kisbAlt/espSkipper_v2/espSkipper2_firmware/src/display/David_Sans8pt7b.h

const uint8_t David_Sans8pt7bBitmaps[] PROGMEM = {
  0x00, 0xFF, 0xFF, 0xFF, 0x0F, 0xCF, 0x3C, 0xF3, 0x30, 0xC3, 0x0C, 0x30,
  0xC3, 0x0C, 0xFF, 0xFF, 0xFF, 0x30, 0xC3, 0x0C, 0xFF, 0xFF, 0xFF, 0x30,
  0xC3, 0x0C, 0x30, 0xC3, 0x0C, 0x0C, 0x03, 0x03, 0xF0, 0xFC, 0xCC, 0xF3,
  0x3C, 0xC3, 0x30, 0x3C, 0x0F, 0x00, 0xF0, 0x3C, 0x0C, 0xC3, 0x3C, 0xCF,
  0x33, 0x3F, 0x0F, 0xC0, 0xC0, 0x30, 0x30, 0x30, 0x30, 0x30, 0xCC, 0x30,
  0xCC, 0x30, 0xCC, 0xC0, 0xCC, 0xC0, 0x30, 0xC0, 0x30, 0xC0, 0x03, 0x0C,
  0x03, 0x0C, 0x03, 0x33, 0x03, 0x33, 0x0C, 0x33, 0x0C, 0x33, 0x0C, 0x0C,
  0x0C, 0x0C, 0x0F, 0x00, 0x0F, 0x00, 0x30, 0xC0, 0x30, 0xC0, 0x30, 0xC0,
  0x30, 0xC0, 0x0F, 0x00, 0x0F, 0x00, 0x33, 0x3C, 0x33, 0x3C, 0xC0, 0xC0,
  0xC0, 0xC0, 0xC0, 0xC3, 0xC0, 0xC3, 0x3F, 0x3C, 0x3F, 0x3C, 0xFF, 0x0C,
  0x33, 0x0C, 0xC3, 0x0C, 0x30, 0xC3, 0x0C, 0x30, 0xC3, 0x0C, 0x30, 0x30,
  0xC0, 0xC3, 0xC3, 0x03, 0x0C, 0x0C, 0x30, 0xC3, 0x0C, 0x30, 0xC3, 0x0C,
  0x30, 0xC3, 0x30, 0xCC, 0x30, 0x0C, 0x03, 0x0F, 0xFF, 0xFF, 0x0C, 0x03,
  0x03, 0x30, 0xCC, 0x0C, 0x03, 0x00, 0xC0, 0x30, 0xFF, 0xFF, 0xF0, 0xC0,
  0x30, 0x0C, 0x03, 0x00, 0xFF, 0x33, 0xCC, 0xFF, 0xF0, 0xF0, 0x03, 0x03,
  0x03, 0x03, 0x0C, 0x0C, 0x0C, 0x0C, 0x30, 0x30, 0x30, 0x30, 0xC0, 0xC0,
  0xC0, 0xC0, 0x3F, 0x0F, 0xCC, 0x0F, 0x03, 0xC0, 0xF0, 0x3C, 0x0F, 0x03,
  0xC0, 0xF0, 0x3C, 0x0F, 0x03, 0xC0, 0xF0, 0x33, 0xF0, 0xFC, 0xFF, 0x33,
  0x33, 0x33, 0x33, 0x33, 0x33, 0x33, 0x3F, 0x0F, 0xCC, 0x0F, 0x03, 0x00,
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
  {   621,  12,  16,  14,    0,  -15 },   // 0x46 'F'
  {   645,  14,  16,  16,    0,  -15 },   // 0x47 'G'
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

const GFXfont David_Sans8pt7b PROGMEM = {
  (uint8_t  *)David_Sans8pt7bBitmaps,
  (GFXglyph *)David_Sans8pt7bGlyphs,
  0x20, 0x7E, 15 };

// Approx. 2305 bytes
