kisbAlt/espSkipper_v2/espSkipper2_firmware/src/display/m2020pt7b.h

const uint8_t m2020pt7bBitmaps[] PROGMEM = {
  0x00, 0x00, 0x00, 0x00, 0x00, 0x00, 0x00, 0x00, 0x00, 0x00, 0x00, 0x00,
  0x00, 0xFF, 0xFF, 0xFF, 0xFF, 0xFF, 0xFF, 0xFF, 0xFF, 0xFF, 0xFF, 0xFF,
  0xFF, 0xFF, 0xFF, 0xFF, 0xFC, 0xFF, 0xFF, 0xFF, 0xFF, 0xF0, 0x00, 0x07,
  0xFF, 0x00, 0x3F, 0xF8, 0x07, 0xFF, 0xF0, 0x3F, 0xFF, 0x83, 0xFF, 0xFE,
  0x7F, 0xFF, 0xFF, 0xFF, 0xFF, 0xFF, 0xE0, 0xFF, 0xFC, 0x07, 0xFF, 0xE0,
  0x3F, 0xFF, 0x01, 0xFF, 0xF8, 0x0F, 0xFF, 0xC0, 0xFF, 0xFE, 0x07, 0xFF,
  0xF0, 0x3F, 0xFF, 0x87, 0xFF, 0xFC, 0x3F, 0xFF, 0xE1, 0xFF, 0xFF, 0x3E,
  0x7F, 0xF9, 0xF3, 0xFF, 0xCF, 0x9F, 0xFF, 0xF0, 0xFF, 0xFF, 0x87, 0xFF,
  0xFC, 0x3F, 0xFF, 0xE1, 0xFF, 0xFC, 0x0F, 0xFF, 0xE0, 0x7F, 0xFF, 0x03,
  0xFF, 0xF0, 0x1F, 0xFF, 0x80, 0xFF, 0xFC, 0x07, 0xFF, 0xE0, 0xFF, 0xFF,
  0x07, 0xFF, 0xFF, 0xFF, 0xCF, 0xFF, 0xF8, 0x7F, 0xFF, 0xC1, 0xFF, 0xFC,
  0x03, 0xFF, 0x80, 0x1F, 0xFC, 0x00, 0xFF, 0xFF, 0xFF, 0xFF, 0xFF, 0xFF,
  0xFF, 0xFF, 0xFC, 0x7F, 0x1F, 0xC7, 0xF1, 0xFC, 0x7F, 0x1F, 0xC7, 0xF1,
  0xFC, 0x7F, 0x1F, 0xC7, 0xF1, 0xFC, 0x7F, 0x1F, 0xC7, 0xF1, 0xFC, 0x7F,
  0x1F, 0xC7, 0xF1, 0xFC, 0x7F, 0x1F, 0xC7, 0xF1, 0xFC, 0x7F, 0x1F, 0xC7,
  0xF1, 0xFC, 0x7F, 0x1F, 0xC7, 0xF1, 0xFC, 0xFF, 0xFC, 0x1F, 0xFF, 0xE3,
  0xFF, 0xFC, 0x7F, 0xFF, 0xEF, 0xFF, 0xFF, 0xFF, 0xFF, 0xC0, 0x07, 0xF8,
  0x00, 0xFF, 0x00, 0x07, 0xE0, 0x00, 0xFC, 0x00, 0x1F, 0x80, 0x03, 0xF0,
  0x01, 0xFE, 0x00, 0x3F, 0xC0, 0x3F, 0xF0, 0x3F, 0xFE, 0x07, 0xFF, 0x03,
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
  {  1521,  21,  39,  26,    0,  -38 },   // 0x46 'F'
  {  1624,  21,  39,  26,    0,  -38 },   // 0x47 'G'
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

const GFXfont m2020pt7b PROGMEM = {
  (uint8_t  *)m2020pt7bBitmaps,
  (GFXglyph *)m2020pt7bGlyphs,
  0x20, 0x7E, 39 };

// Approx. 6848 bytes
