kisbAlt/espSkipper_v2/espSkipper2_firmware/src/display/pf_ronda_seven8pt7b.h

const uint8_t pf_ronda_seven8pt7bBitmaps[] PROGMEM = {
  0x00, 0xFF, 0xFF, 0xF0, 0xF0, 0xCF, 0x3C, 0xF3, 0x33, 0x0C, 0xC3, 0x30,
  0xCC, 0xFF, 0xFF, 0xF3, 0x30, 0xCC, 0xFF, 0xFF, 0xF3, 0x30, 0xCC, 0x33,
  0x0C, 0xC0, 0x0C, 0x03, 0x03, 0xF1, 0xFE, 0xCC, 0xF3, 0x3C, 0xC3, 0x30,
  0x7F, 0x0F, 0xE0, 0xCC, 0x33, 0xCC, 0xF3, 0x37, 0xF8, 0xFC, 0x0C, 0x03,
  0x00, 0x30, 0x0D, 0xE0, 0x3C, 0xC3, 0x33, 0x0C, 0x78, 0xC0, 0xC3, 0x00,
  0x30, 0x00, 0xC0, 0x0C, 0x30, 0x31, 0xE3, 0x0C, 0xCC, 0x33, 0xC0, 0x7B,
  0x00, 0xC0, 0x3C, 0x1F, 0x8C, 0x33, 0x0C, 0xCE, 0x33, 0x07, 0x0C, 0xC3,
  0xCC, 0xF3, 0xBC, 0x33, 0x0C, 0x7E, 0xCF, 0x30, 0xFF, 0x0C, 0x33, 0x0C,
  0xE3, 0x0C, 0x30, 0xC3, 0x0C, 0x30, 0xC3, 0x83, 0x0C, 0x0C, 0x30, 0xC3,
  0x03, 0x0C, 0x1C, 0x30, 0xC3, 0x0C, 0x30, 0xC3, 0x0C, 0x73, 0x0C, 0xC3,
  0x00, 0x0C, 0x03, 0x0C, 0xCF, 0x33, 0x3F, 0x0F, 0xCC, 0xCF, 0x33, 0x0C,
  0x03, 0x00, 0x0C, 0x03, 0x00, 0xC0, 0x30, 0xFF, 0xFF, 0xF0, 0xC0, 0x30,
  0x0C, 0x03, 0x00, 0x33, 0x33, 0xEC, 0xFF, 0xF0, 0xF0, 0x00, 0xC0, 0x30,
  0x0C, 0x07, 0x03, 0x00, 0xC0, 0x30, 0x1C, 0x0C, 0x03, 0x03, 0x80, 0xC0,
  0x30, 0x0C, 0x0E, 0x03, 0x00, 0xC0, 0x30, 0x00, 0x3F, 0x1F, 0xEC, 0x0F,
  0x03, 0xC0, 0xF0, 0x3C, 0x0F, 0x03, 0xC0, 0xF0, 0x3C, 0x0F, 0x03, 0x7F,
  0x8F, 0xC0, 0xFF, 0x33, 0x33, 0x33, 0x33, 0x33, 0x33, 0x3F, 0x1F, 0xEC,
  0x0F, 0x03, 0x00, 0xC0, 0x30, 0x38, 0x0C, 0x0C, 0x03, 0x03, 0x00, 0xC0,
  0xFF, 0xFF, 0xF0, 0x3F, 0x1F, 0xEC, 0x0F, 0x03, 0x00, 0xC0, 0x31, 0xF8,
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
  {   520,  10,  14,  12,    0,  -13 },   // 0x46 'F'
  {   538,  10,  14,  12,    0,  -13 },   // 0x47 'G'
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

const GFXfont pf_ronda_seven8pt7b PROGMEM = {
  (uint8_t  *)pf_ronda_seven8pt7bBitmaps,
  (GFXglyph *)pf_ronda_seven8pt7bGlyphs,
  0x20, 0x7E, 27 };

// Approx. 1950 bytes
