kisbAlt/espSkipper_v2/espSkipper2_firmware/src/instrumentDataModel.cpp

#include "instrumentDataModel.hpp"
#include "stringTranslator.hpp"
#include "instrumentDataFormats.hpp"

SensorUnitEnum InstrumentDataModel::GetCurrentUnitForSensor(SensorId id) const
{
    SensorUnitEnum settingsUnit;
    switch (data[static_cast<size_t>(id)].unit.GetUnitType())
    {
        case UnitType::Speed:
            settingsUnit = static_cast<SensorUnitEnum>(settings.GetValue<uint8_t>(SettingsKey::SpeedUnit));
            break;
        case UnitType::Distance:
            settingsUnit = static_cast<SensorUnitEnum>(settings.GetValue<uint8_t>(SettingsKey::DistanceUnit));
            break;
        default:
            settingsUnit = data[static_cast<size_t>(id)].unit.GetUnitEnum();
    }
    return settingsUnit;
}

InstrumentDataModel::InstrumentDataModel(const Settings &settings) : settings(settings)
{
}

void InstrumentDataModel::UpdateSensor(SensorId id, SensorValue val)
{
    data[static_cast<size_t>(id)].UpdateValue(val);
}

void InstrumentDataModel::UpdateSensorIfLarger(SensorId id, SensorValue val)
{
    std::visit([&val, this, id](auto &currentVal)
               {
        using T = std::decay_t<decltype(currentVal)>;
        
        if constexpr (std::is_arithmetic_v<T>) {
            const T newVal = std::get<T>(val);
            if(!data[static_cast<size_t>(id)].hasData ||static_cast<T>(currentVal < newVal)) {
                data[static_cast<size_t>(id)].UpdateValue(newVal);
            }
        } }, data[static_cast<size_t>(id)].value);
}

void InstrumentDataModel::UpdateSensorIfSmaller(SensorId id, SensorValue val)
{
    std::visit([&val, this, id](auto &currentVal)
               {
        using T = std::decay_t<decltype(currentVal)>;
        
        if constexpr (std::is_arithmetic_v<T>) {
            const T newVal = std::get<T>(val);
            if(!data[static_cast<size_t>(id)].hasData || static_cast<T>(currentVal > newVal)) {
                data[static_cast<size_t>(id)].UpdateValue(newVal);
            }
        } }, data[static_cast<size_t>(id)].value);
}

void InstrumentDataModel::AddSensor(SensorId id, SensorValue val, SensorUnit unit, TextKey titleKey, bool isAverage)
{
    data[static_cast<size_t>(id)] = {id, val, titleKey, unit, isAverage};
}

bool InstrumentDataModel::IsSensorEnabled(SensorId id) const
{
    return !settings.IsSensorDisabled(id);
}

bool InstrumentDataModel::SensorHasData(SensorId id) const
{
    return data[static_cast<size_t>(id)].hasData;
}

SensorValue InstrumentDataModel::GetSensorValue(SensorId id) const
{
    return data[static_cast<size_t>(id)].value;
}

SensorValue InstrumentDataModel::GetSensorValueInUnit(SensorId id, SensorUnitEnum targetUnitEnum) const
{
    return data[static_cast<size_t>(id)].GetValueInUnit(targetUnitEnum);
}

TextKey InstrumentDataModel::GetSensorTitleKey(SensorId id) const
{
    return data[static_cast<size_t>(id)].titleKey;
}

bool InstrumentDataModel::IsSensorEnabledAndHasData(SensorId id) const
{
    return IsSensorEnabled(id) && SensorHasData(id);
}

std::vector<std::pair<SensorId, SensorValue>> InstrumentDataModel::GetDisplaySnapshot() const
{
    std::vector<std::pair<SensorId, SensorValue>> snapshot;

    for (size_t i = 0; i < data.size(); ++i)
    {
        if (data[i].hasData)
        {
            snapshot.push_back({static_cast<SensorId>(i), data[i].value});
        }
    }
    return snapshot;
}

int InstrumentDataModel::GetActiveSensorCount() const
{
    int count = 0;
    const int size = static_cast<int>(SensorId::MAX_SENSORS);
    for (size_t i = 0; i < static_cast<int>(SensorId::MAX_SENSORS); ++i)
    {
        if (IsSensorEnabledAndHasData(static_cast<SensorId>(i)))
        {
            count++;
        }
    }
    return count;
}

void InstrumentDataModel::Reload()
{
}

void InstrumentDataModel::WriteCurrentUnitString(char *unitString, size_t bufferSize, SensorId id) const
{
    SensorUnitEnum settingsUnit = GetCurrentUnitForSensor(id);
    strncpy(unitString, GetUnitString(settingsUnit), bufferSize - 1);
    unitString[bufferSize - 1] = '\0';
}

SensorValue InstrumentDataModel::GetSensorValueCurrentUnit(SensorId id) const
{
    SensorUnitEnum settingsUnit = GetCurrentUnitForSensor(id);
    return data[static_cast<size_t>(id)].GetValueInUnit(settingsUnit);
}

SensorUnit::SensorUnit() : sensorUnit(SensorUnitEnum::BlankUnit)
{
}

SensorUnit::SensorUnit(SensorUnitEnum sensorUnitEnum) : sensorUnit(sensorUnitEnum)
{
}

const char *SensorUnit::GetString()
{
    return GetUnitString(sensorUnit);
}
UnitType SensorUnit::GetUnitType(SensorUnitEnum sensorUnitEnum) const
{
    switch (sensorUnitEnum)
    {
    case SensorUnitEnum::Kmph:
    case SensorUnitEnum::Mps:
    case SensorUnitEnum::Knots:
        return UnitType::Speed;
    case SensorUnitEnum::Kilometer:
    case SensorUnitEnum::Meter:
    case SensorUnitEnum::Feet:
        return UnitType::Distance;
    case SensorUnitEnum::Celsius:
        return UnitType::Temperature;
    case SensorUnitEnum::Degrees:
        return UnitType::Angle;
    case SensorUnitEnum::BlankUnit:
    default:
        return UnitType::None;
    }
};

UnitType SensorUnit::GetUnitType() const
{
    return GetUnitType(sensorUnit);
}

bool SensorUnit::IsSameUnitType(SensorUnitEnum sensorUnitEnum) const
{
    return GetUnitType() == GetUnitType(sensorUnitEnum);
}

void InstrumentDataModel::SensorRecord::UpdateValue(SensorValue newValue)
{
    if (!isAverage || !hasData)
    {
        value = newValue;
        dataCount = isAverage ? 1 : 0;
        hasData = true;
        return;
    }

    dataCount++;
    std::visit([&newValue, this](auto &currentVal)
               {
        using T = std::decay_t<decltype(currentVal)>;
        
        if constexpr (std::is_arithmetic_v<T>) {
            const T newVal = std::get<T>(newValue);
            
            currentVal = static_cast<T>(currentVal + (newVal - currentVal) / static_cast<float>(dataCount));
        } }, value);
}

SensorValue InstrumentDataModel::SensorRecord::GetValueInUnit(SensorUnitEnum targetUnitEnum) const
{
    if (unit.GetUnitEnum() == targetUnitEnum)
    {
        return value;
    }

    if (!unit.IsSameUnitType(targetUnitEnum) || unit.GetUnitType() == UnitType::None)
    {
        return value;
    }

    return std::visit([this, targetUnitEnum](auto &&arg) -> SensorValue
                      {
        using T = std::decay_t<decltype(arg)>;
        
        if constexpr (std::is_same_v<T, float> || std::is_same_v<T, int>) {
            
            float val = static_cast<float>(arg);
            float convertedVal = val;

            // base unit => mps
            if (unit.GetUnitType() == UnitType::Speed) {
                float mps = val;
                
                switch (unit.GetUnitEnum()) {
                    case SensorUnitEnum::Kmph:  mps = val / 3.6f; break;
                    case SensorUnitEnum::Knots: mps = val * 0.514444f; break;
                    case SensorUnitEnum::Mps:   mps = val; break;
                    default: break;
                }
                
                switch (targetUnitEnum) {
                    case SensorUnitEnum::Kmph:  convertedVal = mps * 3.6f; break;
                    case SensorUnitEnum::Knots: convertedVal = mps / 0.514444f; break;
                    case SensorUnitEnum::Mps:   convertedVal = mps; break;
                    default: break;
                }
            }
            // base unit => meters
            else if (unit.GetUnitType() == UnitType::Distance) {
                float meters = val;

                switch (unit.GetUnitEnum()) {
                    case SensorUnitEnum::Kilometer: meters = val * 1000.0f; break;
                    case SensorUnitEnum::Feet:      meters = val * 0.3048f; break;
                    case SensorUnitEnum::Meter:     meters = val; break;
                    default: break;
                }
                
                switch (targetUnitEnum) {
                    case SensorUnitEnum::Kilometer: convertedVal = meters / 1000.0f; break;
                    case SensorUnitEnum::Feet:      convertedVal = meters / 0.3048f; break;
                    case SensorUnitEnum::Meter:     convertedVal = meters; break;
                    default: break;
                }
            }
            
            return convertedVal;

        } else {
            return arg;
        } }, value);
}
