kisbAlt/espSkipper_v2/espSkipper2_firmware/src/display/pf_ronda_seven4pt7b.h

const uint8_t pf_ronda_seven4pt7bBitmaps[] PROGMEM = {
  0x00, 0xFA, 0xB4, 0x52, 0xBE, 0xAF, 0xA9, 0x40, 0x23, 0xAB, 0x47, 0x16,
  0xAE, 0x20, 0x43, 0x49, 0x20, 0x82, 0x49, 0x61, 0x00, 0x64, 0xA8, 0x9A,
  0xC9, 0xA0, 0xC0, 0x2A, 0x49, 0x22, 0x20, 0x88, 0x92, 0x4A, 0x80, 0x25,
  0x5D, 0x52, 0x00, 0x21, 0x3E, 0x42, 0x00, 0x58, 0xE0, 0x80, 0x08, 0x44,
  0x22, 0x21, 0x10, 0x80, 0x74, 0x63, 0x18, 0xC5, 0xC0, 0xD5, 0x54, 0x74,
  0x42, 0x22, 0x23, 0xE0, 0x74, 0x42, 0x60, 0xC5, 0xC0, 0x32, 0x95, 0x2F,
  0x88, 0x40, 0xFC, 0x21, 0xE0, 0xC5, 0xC0, 0x74, 0x61, 0xE8, 0xC5, 0xC0,
  0xF8, 0x44, 0x22, 0x11, 0x00, 0x74, 0x62, 0xE8, 0xC5, 0xC0, 0x74, 0x62,
  0xF0, 0xC5, 0xC0, 0x88, 0x40, 0x58, 0x2A, 0x22, 0xE3, 0x80, 0x88, 0xA8,
  0x74, 0x42, 0x22, 0x00, 0x80, 0x3C, 0x42, 0x9D, 0xA5, 0xA5, 0xAD, 0x95,
  0x42, 0x38, 0x74, 0x63, 0xF8, 0xC6, 0x20, 0xF4, 0x63, 0xE8, 0xC7, 0xC0,
  0x74, 0x61, 0x08, 0x45, 0xC0, 0xF4, 0x63, 0x18, 0xC7, 0xC0, 0xFC, 0x21,
  0xE8, 0x43, 0xE0, 0xFC, 0x21, 0xE8, 0x42, 0x00, 0x74, 0x61, 0x78, 0xCD,
  0xA0, 0x8C, 0x63, 0xF8, 0xC6, 0x20, 0xFE, 0x11, 0x11, 0x19, 0x60, 0x8C,
  0xA9, 0x8A, 0x4A, 0x20, 0x88, 0x88, 0x88, 0xF0, 0x83, 0x8E, 0xAC, 0x98,
  0x30, 0x60, 0x80, 0x8E, 0x6B, 0x5A, 0xCE, 0x20, 0x74, 0x63, 0x18, 0xC5,
  0xC0, 0xF4, 0x63, 0xE8, 0x42, 0x00, 0x74, 0x63, 0x18, 0xC5, 0xC1, 0xF4,
  0x63, 0xEA, 0x4A, 0x20, 0x74, 0x60, 0xE0, 0xC5, 0xC0, 0xF9, 0x08, 0x42,
  0x10, 0x80, 0x8C, 0x63, 0x18, 0xC5, 0xC0, 0x8C, 0x54, 0xA5, 0x10, 0x80,
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
  {   147,   5,   7,   6,    0,   -6 },   // 0x46 'F'
  {   152,   5,   7,   6,    0,   -6 },   // 0x47 'G'
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

const GFXfont pf_ronda_seven4pt7b PROGMEM = {
  (uint8_t  *)pf_ronda_seven4pt7bBitmaps,
  (GFXglyph *)pf_ronda_seven4pt7bGlyphs,
  0x20, 0x7E, 13 };

// Approx. 1033 bytes
