kisbAlt/espSkipper_v2/espSkipper2_firmware/src/accelerometerHandler.hpp

#include "pinout.hpp"
#include "instrumentDataModel.hpp"
class AccelerometerHandler {
private:
    InstrumentDataModel& dataModel;
public:
    AccelerometerHandler(InstrumentDataModel& dataModel);
    void Init();
    void ReadAccelerometerData();
    void Reload();
};
