kisbAlt/espSkipper_v2/espSkipper2_firmware/src/display/SimplyMono_Bold50pt7b.h

const uint8_t SimplyMono_Bold50pt7bBitmaps[] PROGMEM = {
  0x00, 0x1F, 0xFE, 0x1F, 0xFF, 0x8F, 0xFF, 0xC7, 0xFF, 0xE3, 0xFF, 0xF1,
  0xFF, 0xF8, 0xFF, 0xFC, 0x7F, 0xFE, 0x3F, 0xFF, 0x1F, 0xFF, 0x8F, 0xFF,
  0xC7, 0xFF, 0xE3, 0xFF, 0xF1, 0xFF, 0xF8, 0xFF, 0xFC, 0x3F, 0xFE, 0x1F,
  0xFF, 0x0F, 0xFF, 0x87, 0xFF, 0xC3, 0xFF, 0xE1, 0xFF, 0xF0, 0xFF, 0xF8,
  0x7F, 0xFC, 0x3F, 0xFE, 0x1F, 0xFF, 0x0F, 0xFF, 0x87, 0xFF, 0xC3, 0xFF,
  0xE1, 0xFF, 0xF0, 0xFF, 0xF8, 0x7F, 0xFC, 0x3F, 0xFE, 0x1F, 0xFF, 0x0F,
  0xFF, 0x07, 0xFF, 0x83, 0xFF, 0xC1, 0xFF, 0xE0, 0x7F, 0xF0, 0x3F, 0xF8,
  0x1F, 0xFC, 0x0F, 0xFE, 0x07, 0xFF, 0x03, 0xFF, 0x81, 0xFF, 0xC0, 0xFF,
  0xE0, 0x7F, 0xF0, 0x3F, 0xF8, 0x1F, 0xFC, 0x0F, 0xFE, 0x07, 0xFF, 0x01,
  0xFF, 0x00, 0x00, 0x00, 0x00, 0x00, 0x00, 0x00, 0x00, 0x00, 0x00, 0x00,
  0x03, 0xF0, 0x07, 0xFE, 0x07, 0xFF, 0x87, 0xFF, 0xC7, 0xFF, 0xF3, 0xFF,
  0xFB, 0xFF, 0xFF, 0xFF, 0xFF, 0xFF, 0xFF, 0xFF, 0xFF, 0xFF, 0xFF, 0xFF,
  0xFF, 0xF7, 0xFF, 0xF1, 0xFF, 0xF8, 0x7F, 0xF8, 0x1F, 0xF8, 0x03, 0xF0,
  0x00, 0x7F, 0xF0, 0x0F, 0xFE, 0xFF, 0xF8, 0x1F, 0xFF, 0xFF, 0xF8, 0x1F,
  0xFF, 0xFF, 0xF8, 0x1F, 0xFF, 0xFF, 0xF8, 0x1F, 0xFF, 0xFF, 0xF8, 0x1F,
  0xFF, 0xFF, 0xF8, 0x1F, 0xFF, 0xFF, 0xF8, 0x1F, 0xFF, 0xFF, 0xF8, 0x1F,
  0xFF, 0xFF, 0xF8, 0x1F, 0xFF, 0xFF, 0xF8, 0x1F, 0xFF, 0x7F, 0xF0, 0x0F,
  0xFE, 0x7F, 0xF0, 0x0F, 0xFE, 0x7F, 0xF0, 0x0F, 0xFE, 0x7F, 0xF0, 0x0F,
  0xFE, 0x7F, 0xF0, 0x0F, 0xFE, 0x7F, 0xF0, 0x0F, 0xFE, 0x7F, 0xF0, 0x0F,
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
  { 12466,  41,  72,  57,    9,  -71 },   // 0x46 'F'
  { 12835,  50,  74,  57,    4,  -72 },   // 0x47 'G'
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

const GFXfont SimplyMono_Bold50pt7b PROGMEM = {
  (uint8_t  *)SimplyMono_Bold50pt7bBitmaps,
  (GFXglyph *)SimplyMono_Bold50pt7bGlyphs,
  0x20, 0x7E, 129 };

// Approx. 34288 bytes
